Kronos3/rit-msd-werfen/pcb/WerfenMc/c8e72fd6bf5f4ed4a876ba1fe98828bc.png

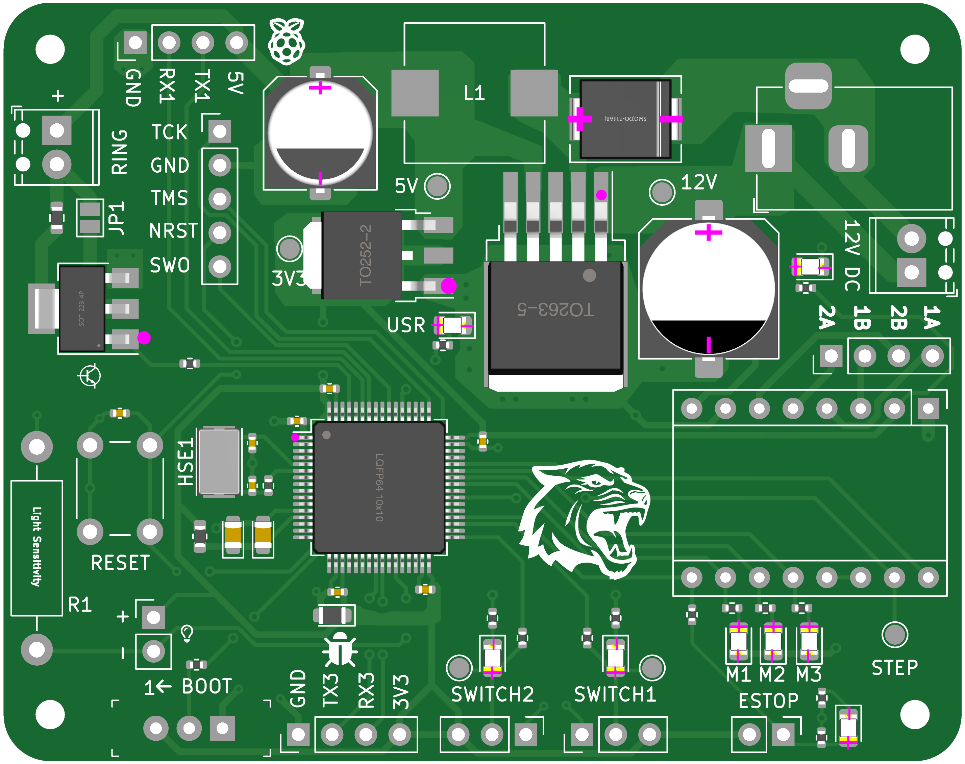
pcb/WerfenMc/c8e72fd6bf5f4ed4a876ba1fe98828bc.png
