Kronos3/rit-msd-werfen/prototyping/300574256.jpg

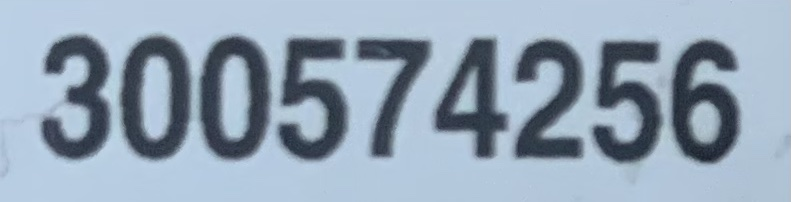
prototyping/300574256.jpg
