Kronos3/rit-msd-werfen/prototyping/300574256_processed.jpg

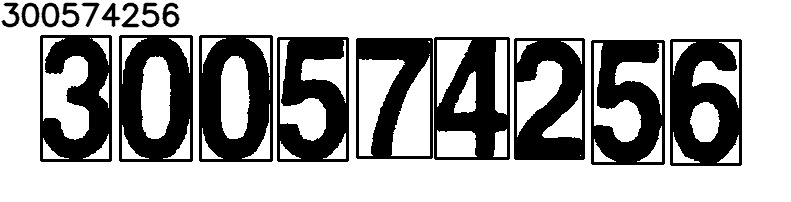
prototyping/300574256_processed.jpg
