Kronos3/rit-msd-werfen/prototyping/300574484.jpg

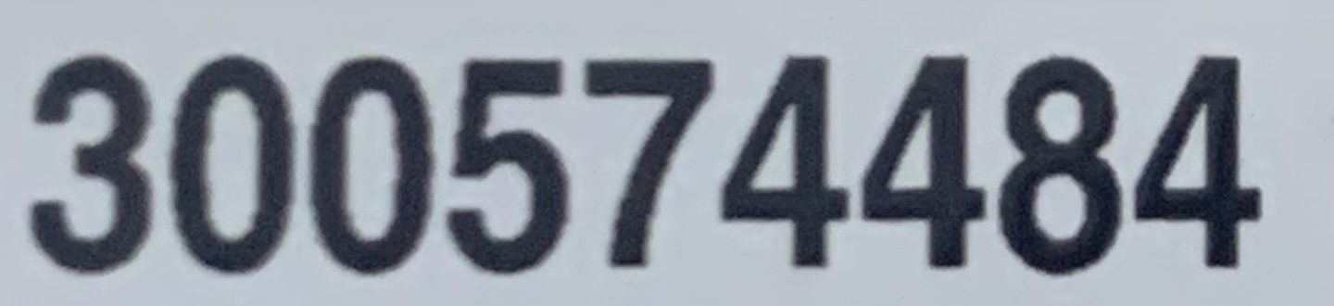
prototyping/300574484.jpg
