Kronos3/rit-msd-werfen/prototyping/300574484_processed.jpg

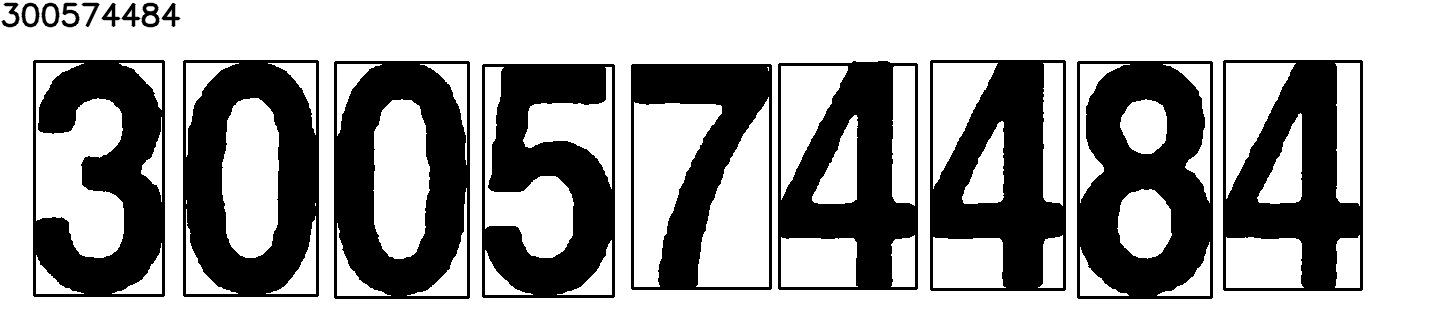
prototyping/300574484_processed.jpg
