Kronos3/rit-msd-werfen/prototyping/edge.jpeg

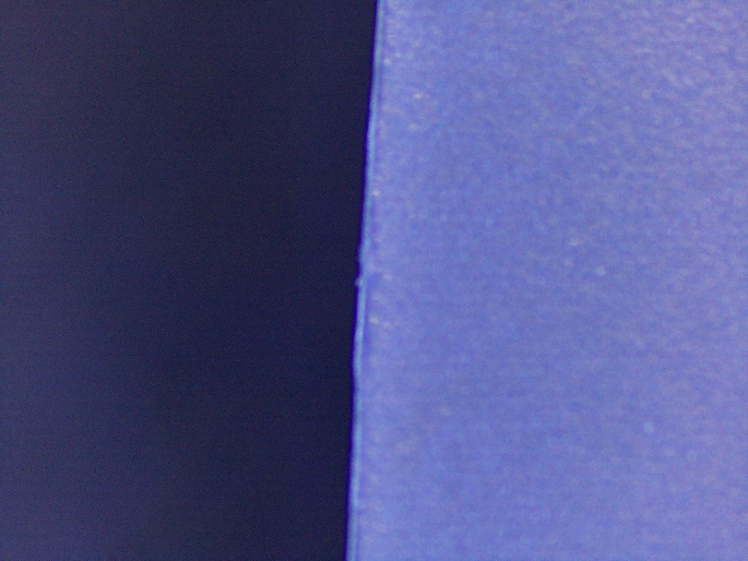
prototyping/edge.jpeg
