Kronos3/rit-msd-werfen/prototyping/gold_kernel.png

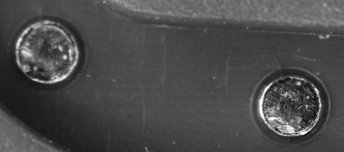
prototyping/gold_kernel.png
