Kronos3/rit-msd-werfen/prototyping/kernel.jpeg

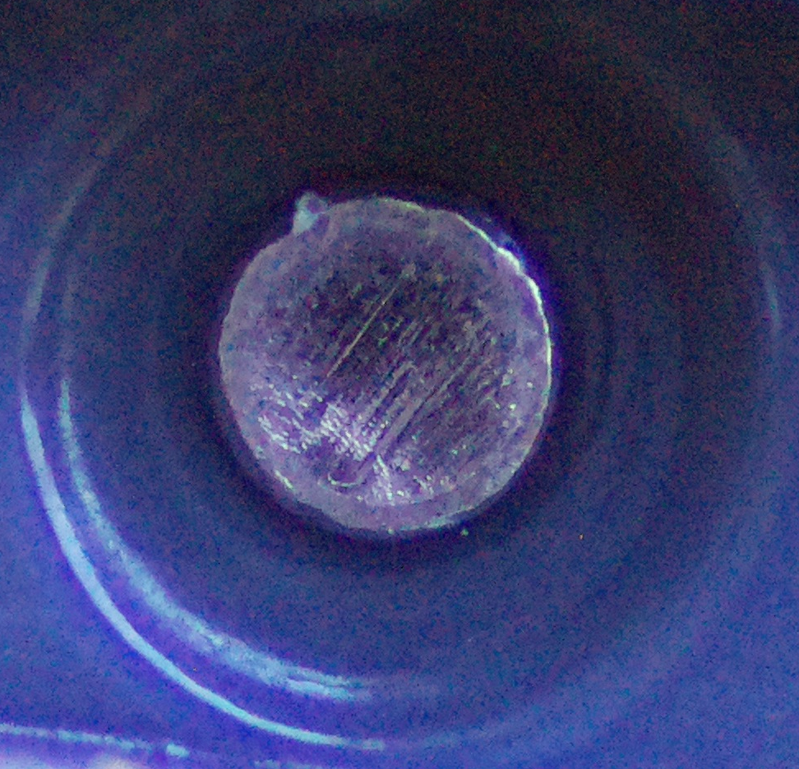
prototyping/kernel.jpeg
