Kronos3/rit-msd-werfen/prototyping/non-edge.jpeg

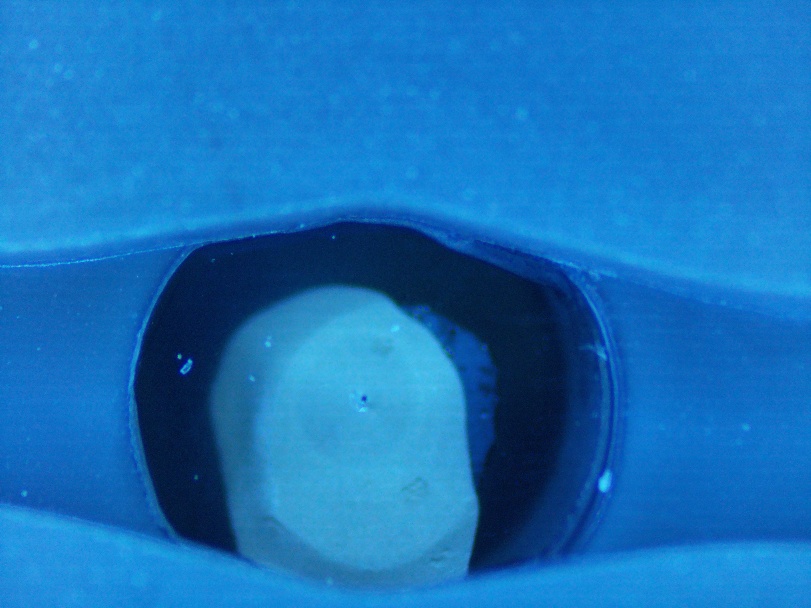
prototyping/non-edge.jpeg
