Kronos3/rit-msd-werfen/prototyping/pic2.jpeg

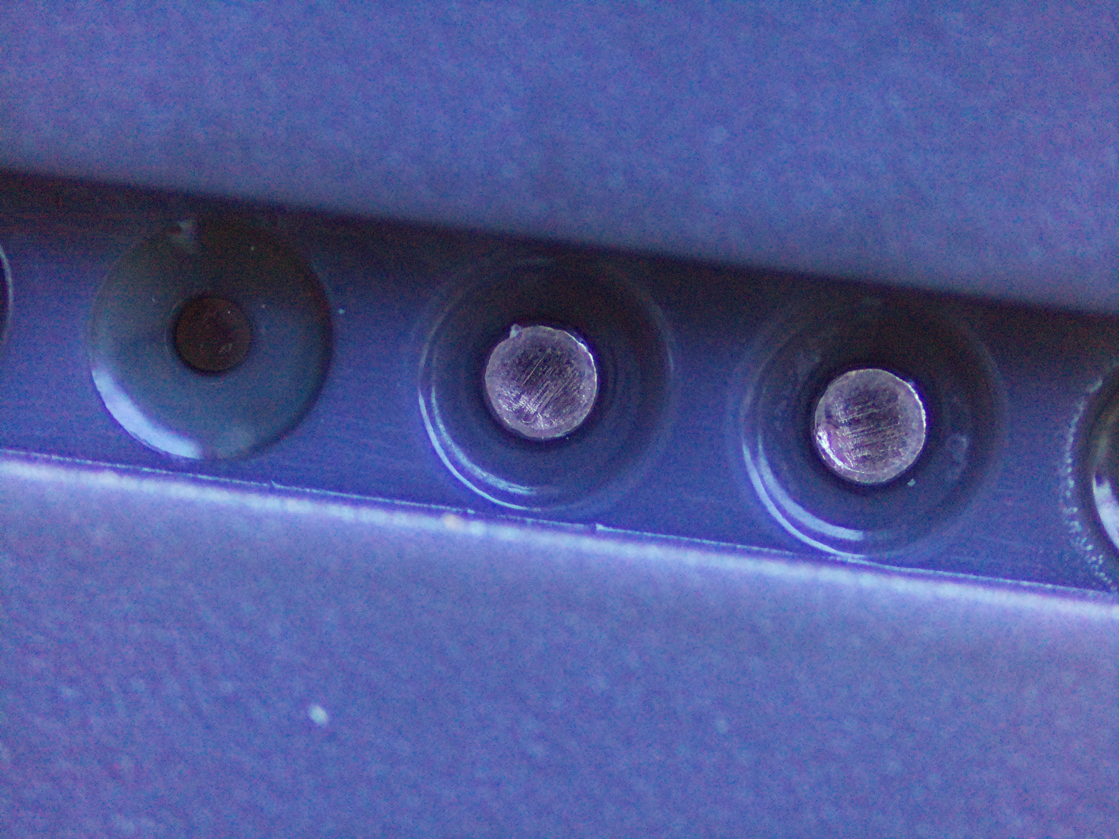
prototyping/pic2.jpeg
