Kronos3/rit-msd-werfen/prototyping/pic2_processed.jpeg

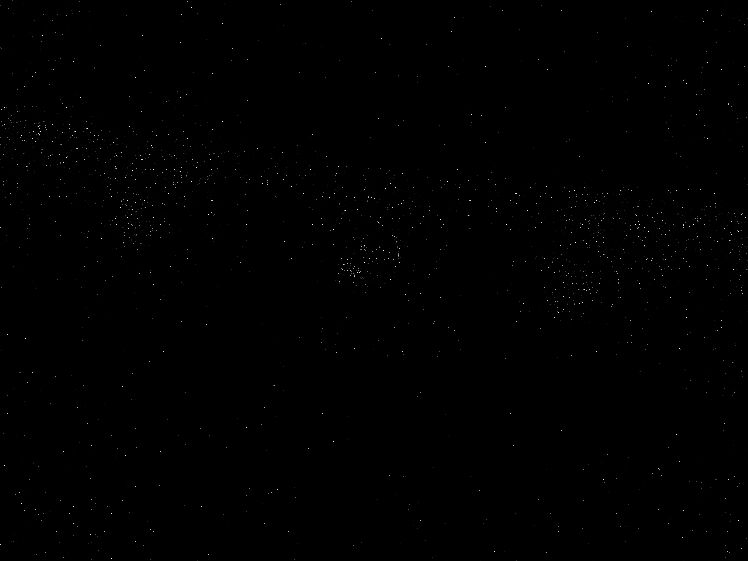
prototyping/pic2_processed.jpeg
