Kronos3/rit-msd-werfen/prototyping/werfen_text.png

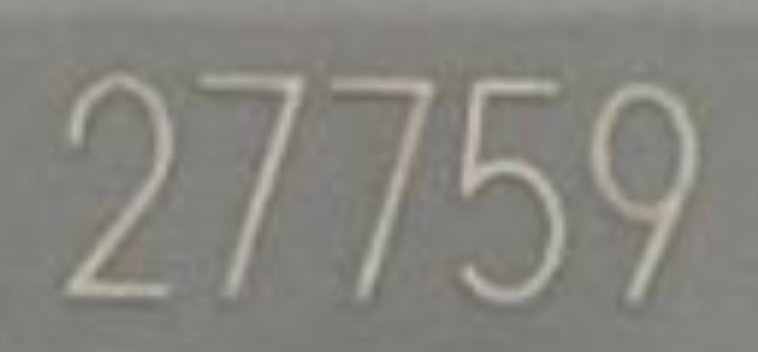
prototyping/werfen_text.png
