Kronos3/rit-msd-werfen/mc/Core/Inc/main.h

#define LIGHT_S_Pin GPIO_PIN_1
#define LIGHT_S_GPIO_Port GPIOB
#define SWITCH2_Pin GPIO_PIN_12
#define SWITCH2_GPIO_Port GPIOB
#define SWITCH2_EXTI_IRQn EXTI15_10_IRQn
#define SWITCH1_Pin GPIO_PIN_14
#define SWITCH1_GPIO_Port GPIOB
#define SWITCH1_EXTI_IRQn EXTI15_10_IRQn
#define ENABLE_Pin GPIO_PIN_15
#define ENABLE_GPIO_Port GPIOB
#define ENABLE_EXTI_IRQn EXTI15_10_IRQn
#define STEP_Pin GPIO_PIN_8
#define STEP_GPIO_Port GPIOC
#define MS1_Pin GPIO_PIN_8
#define MS1_GPIO_Port GPIOA
#define MS2_Pin GPIO_PIN_9
#define MS2_GPIO_Port GPIOA
#define MS3_Pin GPIO_PIN_10
#define MS3_GPIO_Port GPIOA
#define DIR_Pin GPIO_PIN_11
#define DIR_GPIO_Port GPIOA
#define TMS_Pin GPIO_PIN_13
#define TMS_GPIO_Port GPIOA
#define TCK_Pin GPIO_PIN_14
#define TCK_GPIO_Port GPIOA
#define LED_Pin GPIO_PIN_12
#define LED_GPIO_Port GPIOC
#define SWO_Pin GPIO_PIN_3
#define SWO_GPIO_Port GPIOB
#define LIGHT_Pin GPIO_PIN_8
#define LIGHT_GPIO_Port GPIOB
#define LIGHT_PWM_CHANNEL TIM_CHANNEL_3
#define MOTOR_PWM_CHANNEL TIM_CHANNEL_3
