Kronos3/rit-msd-werfen/src/rit/stage.py

import enum
import logging
import struct
import threading
import time
from typing import Union

import serial

from rit.crc import crc8


log = logging.getLogger(__name__)


class StageOpcode(enum.IntEnum):
    IDLE = 0
    RELATIVE = 1
    ABSOLUTE = 2
    SPEED = 3
    STOP = 4
    SET_POSITION = 5
    GET_POSITION = 6
    LED_PWM = 7
    LED_VOLTAGE = 8
    LED_PID = 9
    SWITCH_DEBOUNCE = 10
    EMERGENCY_STOP = 11
    EMERGENCY_CLEAR = 12
    LIMIT_STEP_OFF = 13


class StageDirection(enum.IntEnum):
    FORWARD = 0
    BACKWARD = 1


class StageFlags(enum.IntFlag):
    PID_P = 0
    PID_I = 1
    PID_D = 2

    MOTOR_IS_REVERSED = 1 << 5,
    MOTOR_IGNORE_LIMITS = 1 << 6

    LIMIT_1 = 1 << 0
    LIMIT_2 = 1 << 1
    ESTOP = 1 << 2
    RUNNING = 1 << 3
    LED = 1 << 4
    FAILURE = 1 << 5
    CALIBRATED = 1 << 6


class StageStepSize(enum.IntEnum):
    FULL = 0
    HALF = 1
    QUARTER = 2
    EIGHTH = 3


class StagePacket:
    opcode: StageOpcode
    arg: Union[int, float]
    flags: int

    def __init__(self, opcode: StageOpcode,
                 arg: Union[int, float] = 0,
                 flags: int = 0):
        self.opcode = opcode
        self.arg = arg
        self.flags = flags

    def encode(self) -> bytes:
        packet_start = struct.pack(
            f"<BBH{'i' if type(self.arg) is int else 'f'}B",
            0xDE, 0xAD,
            self.opcode,
            self.arg,
            self.flags)

        return packet_start + struct.pack(
            "BBB", crc8(packet_start), 0xBE, 0xEF)

    @staticmethod
    def decode(m: bytes) -> 'StagePacket':
        assert len(m) == 12, f"Expected 12 byte packet: f{len(m)}"

        s1, s2, opcode, arg, flags, xsum, e1, e2 = struct.unpack("BBHiBBBB", m)

        assert s1 == 0xDE and s2 == 0xAD, (hex(s1), hex(s2))
        assert e1 == 0xBE and e2 == 0xEF, (hex(e1), hex(e2))

        calculated_crc = crc8(m[:9])
        if calculated_crc != xsum:
            log.warning("Checksum for %s mismatch 0x%02x != 0x%02x",
                        StageOpcode(opcode).name, calculated_crc, xsum)

        return StagePacket(opcode, arg, flags)


class Stage:
    """
    Primary driver to interface with the single axis stage
    Given a UART serial port, all the Tx/Rx operations are
    hidden behind this class
    """

    limit_1: bool
    limit_2: bool
    estop: bool
    running: bool
    led: bool
    failure: bool
    calibrated: bool

    mutex: threading.Lock

    def __init__(self, ser: Union[serial.Serial, None]):
        self.serial = ser

        self.limit_1 = False
        self.limit_2 = False
        self.estop = False
        self.running = False
        self.led = False
        self.failure = False
        self.calibrated = False

        self.mutex = threading.Lock()

        with self.mutex:
            if self.serial:
                self.serial.flush()

    def send(self, pkt: StagePacket):
        """
        Send a packet to the microcontroller and
        wait for a reply.
        :param pkt:
        :return:
        """

        with self.mutex:
            if self.serial:
                self.serial.flush()
                self.serial.reset_input_buffer()
                self.serial.reset_output_buffer()
                self.serial.write(pkt.encode())
                reply_bytes = self.serial.read(12)
            else:
                if pkt.opcode == StageOpcode.SET_POSITION:
                    self.calibrated = True
                reply_bytes = StagePacket(pkt.opcode, 0, StageFlags.CALIBRATED if self.calibrated else 0).encode()

        if len(reply_bytes) < 12:
            raise TimeoutError(f"Stage UART timed out while waiting for a reply to {pkt.opcode.name}")

        reply = StagePacket.decode(reply_bytes)

        self.limit_1 = bool(StageFlags.LIMIT_1 & reply.flags)
        self.limit_2 = bool(StageFlags.LIMIT_2 & reply.flags)
        self.estop = bool(StageFlags.ESTOP & reply.flags)
        self.running = bool(StageFlags.RUNNING & reply.flags)
        self.led = bool(StageFlags.LED & reply.flags)
        self.failure = bool(StageFlags.FAILURE & reply.flags)
        self.calibrated = bool(StageFlags.CALIBRATED & reply.flags)

        return reply

    def idle(self):
        """
        Send an idle packet to the stage
        This is used to update the status flags periodically
        """
        self.send(StagePacket(StageOpcode.IDLE))

    def wait(self,
             timeout: float = 0.0,
             granularity: float = 0.1,
             fault_on_limit: bool = True):
        """
        Wait for a motion to finish by sending idle commands
        until the motor status indicates the motion in complete
        :param timeout: Denotes a timeout (0 for none) when the motor motion should be cancelled
        :param granularity: Denotes how often to check if motor is running
        :param fault_on_limit: Throw assertion failure if motion hit a limit switch
        """
        self.idle()
        start_time = time.time()
        while self.running:
            if (timeout > 0) and ((time.time() - start_time) > timeout):
                self.stop()
                raise TimeoutError(f"Motion timed out after {timeout}s")
            time.sleep(granularity)
            self.idle()

            if fault_on_limit:
                assert not self.failure, "Motor request hit a limit switch"

    def relative(self, n: int, size: StageStepSize, ignore_limits: bool = False):
        """
        Perform a relative motion
        :param n: number of steps
        :param size: size of the stage steps
        :param ignore_limits: Run the motion request even if stuck on a limit switch
        """
        pkt = StagePacket(
            StageOpcode.RELATIVE,
            abs(n),
            (size & 0x0F) | (StageFlags.MOTOR_IS_REVERSED if n < 0 else 0)
            | (StageFlags.MOTOR_IGNORE_LIMITS if ignore_limits else 0)
        )

        self.send(pkt)

    def absolute(self, n: int, size: StageStepSize = StageStepSize.EIGHTH, ignore_limits: bool = False):
        """
        Perform absolute motion to stage position
        using requested step size. The larger the step size
        the faster the motion will happen, but it'll only move to
        multiple of the step size.
        :param n: position to move to
        :param size: step size
        :param ignore_limits: Run the motion request even if stuck on a limit switch
        """
        self.send(StagePacket(StageOpcode.ABSOLUTE, n,
                              size & 0x0F | (StageFlags.MOTOR_IGNORE_LIMITS if ignore_limits else 0)))

    def home(self, direction: StageDirection, size: StageStepSize):
        """
        Move at maximum speed to one of the edges of the stage
        Stops when it hits a limit switch
        :param direction: forward or backwards
        :param size: step size to home motor at
        """
        if direction == StageDirection.FORWARD:
            self.relative(100000, size)
        else:
            self.relative(-100000, size)

    def speed(self, hz: int):
        """
        Set the motor step rate
        :param hz: step rate in hertz
        """
        self.send(StagePacket(StageOpcode.SPEED, hz))

    def stop(self):
        self.send(StagePacket(StageOpcode.STOP))

    def set_position(self, pos: int):
        """
        Set the internal position of the stage to
        another value without moving the stage
        :param pos: position to set current location to
        """
        self.send(StagePacket(StageOpcode.SET_POSITION, pos))

    def get_position(self) -> int:
        """
        Get the current position of the stage
        :return: Current position in 1/8th steps
        """
        reply = self.send(StagePacket(StageOpcode.GET_POSITION))
        return reply.arg

    def led_pwm(self, pwm: float):
        """
        Directly set the PWM light duty cycle.
        :param pwm: duty cycle from 0 to 1.0
        """
        assert 0.0 <= pwm <= 1.0, pwm
        self.send(StagePacket(StageOpcode.LED_PWM, pwm))

    def led_voltage(self, voltage: float):
        """
        Use the internal PID controller to hold the
        light around a voltage reading on the photo-transistor
        ADC circuit.
        :param voltage: Voltage to keep the light level at (0 - 3.3V)
        """
        assert 0.0 <= voltage <= 3.3, f"Voltage must between 0V and 3.3V: {round(voltage, 2)}V"
        self.send(StagePacket(StageOpcode.LED_VOLTAGE, voltage))

    def led_pid_p(self, kp: float):
        """
        Set the proportional gain on the
        voltage PID controller for light level
        :param kp: Kp scalar
        """
        self.send(StagePacket(StageOpcode.LED_PID, kp, StageFlags.PID_P))

    def led_pid_i(self, ki: float):
        """
        Set the integral gain on the
        voltage PID controller for light level
        :param ki: Ki scalar
        """
        self.send(StagePacket(StageOpcode.LED_PID, ki, StageFlags.PID_I))

    def led_pid_d(self, kd: float):
        """
        Set the derivative gain on the
        voltage PID controller for light level
        :param kd: Kd scalar
        """
        self.send(StagePacket(StageOpcode.LED_PID, kd, StageFlags.PID_D))

    def emergency_stop(self):
        """
        Set the E-stop software flag
        This will block all motor requests until the flag
        is cleared. This overrides the hardware signal via software.
        """
        self.send(StagePacket(StageOpcode.EMERGENCY_STOP))

    def emergency_clear(self):
        """
        Clear the software E-stop flag. The hardware signal will
        still remain in effect if on.
        """
        self.send(StagePacket(StageOpcode.EMERGENCY_CLEAR))

    def switch_step_off(self, size: StageStepSize, nsteps: int):
        """
        Set up the limit switch step off motion which is run after
        a limit switch is hit during a motion request
        :param size: Step size
        :param nsteps: number of steps
        """
        self.send(StagePacket(
            StageOpcode.LIMIT_STEP_OFF,
            abs(nsteps),
            (size & 0x0F)
        ))

    def switch_debounce(self, ms: int):
        """
        Set debounce delay on the limit switches.
        This will change the responsiveness of switches but will
        also make them more robust to re-trigger when the stage is moving
        off the limit switch.

        If the stage stops prematurely as it is moving away from a pressed limit
        switch, you may want to increase this number. By default, it is 10ms.
        :param ms: millisecond delay to recheck the switch value after a rising edge
        """
        self.send(StagePacket(StageOpcode.SWITCH_DEBOUNCE, ms))
